wdebeaum/piano-keyboard/end.scad

/* end.scad - controls at the left end of octave.scad
 * William de Beaumont
 * 2020-06-28
 */

include <common.scad>;
include <logo.scad>;

//
// locations and sizes of PCB features
//

// reference point is top left corner of PCB; Y is inverted from KiCAD
// x->width, y->height, z->thickness

// the board itself
pcb_width = 1.62*25.4;
pcb_height = 3.23*25.4;

// Teensy 4.0
teensy_min_x = 0.87*25.4;
teensy_min_y = -0.45*25.4;
teensy_min_z = 0.1*25.4; // ???
teensy_width = 0.7*25.4;
teensy_height = 1.4*25.4;
teensy_thickness = pcb_thickness; // ???
// guessing based on pictures
teensy_led_x = teensy_min_x + 0.5*25.4;
teensy_led_y = teensy_min_y + 0.13*25.4;
teensy_led_radius = 0.1*25.4/2;

// USB receptacle on Teensy 4.0
// (mostly guesswork from generic USB diagram I googled)
usb_width = 7.5;
usb_height = 2.75+3.35;
usb_thickness = 2.5;
// guessing it's centered on Teensy
usb_min_x = teensy_min_x + (teensy_width - usb_width)/2;
usb_max_y = teensy_min_y + teensy_height + 1.3;
usb_min_z = teensy_min_z + teensy_thickness;

// connector to keys
j5_x = pcb_width;
j5_min_y = -1.62*25.4;
j5_height = 0.5*25.4;
j5_thickness = 0.1*25.4;
j5_min_z = -(pcb_thickness+j5_thickness);

// screws
screw1_x = 1.12*25.4;
screw1_y = -1.35*25.4;
screw2_x = 0.67*25.4;
screw2_y = -2.9*25.4;

// buttons
button_radius = 3.51/2; // radius of the part of the button that moves
button_thickness = 5; // height of the top of the button above the pcb
//button_travel = 0.010; // how much the button goes down when pressed
// ^^^ actual value vvv fudged
button_travel = 1.01;
button_width = 6; // width and height of the square box the button is in
// button centers:
//    x1  x2  x3
// y1     sw1
// y2     sw2
// y3 sw3     sw7
// y4     sw6
// y5 sw4
// y6     sw5
button_x1 = 0.24*25.4;
button_x2 = 0.7*25.4;
button_x3 = 1.15*25.4;
button_y1 = -1.24*25.4;
button_y2 = -1.59*25.4;
button_y3 = -1.84*25.4;
button_y4 = -2.1*25.4;
button_y5 = -2.28*25.4;
button_y6 = -2.47*25.4;

// potentiometers
pot_shaft_radius = 6/2;
pot_shaft_max_x = 0.005*25.4;
pot_shaft_length = 20-8; // quoted as 8mm, but that includes pot body
pot_shaft_min_x = pot_shaft_max_x - pot_shaft_length;
pot_flat_length = 7;
pot_flat_depth = 6-4.5; // how far in from where the circumference would be otherwise
pot1_shaft_y = -1.35*25.4;
pot2_shaft_y = -2.9*25.4;
pot_shaft_z = 0.394*25.4;
pot_base_width = 9.7; // along edge of pcb

// sustain pedal jack
sus_radius = 0.1875*25.4;
sus_x = 1.2730*25.4; // center x
sus_y = -pcb_height;
sus_z = 0.492*25.4;
sus_min_x = 0.96*25.4; // left x

// max height above pcb of any component (sustain pedal jack)
top_component_thickness = 0.708*25.4;
// ditto for components on bottom (J5)
//bottom_component_thickness = 0.1*25.4; //unused

//
// other parameters and computed values
//

electronics_height = pcb_height + teensy_height + teensy_min_y;
electronics_thickness = top_component_thickness + support_base_height;
electronics_min_z = -support_base_height;

pcb_y_gap = gap + small_v_hole_shrinkage;

knob_radius = 15;
knob_width = pot_shaft_length - (wall_thickness+2*(gap+sliding_deduction));
knob_min_x = pot_shaft_min_x;
// use thicker outer wall for knobs so that the gap doesn't show much
knob_wall_thickness = 5;
finger_radius = 5;
finger_depth = 2;
knob_ir = pot_shaft_radius + gap/* + small_v_hole_shrinkage*/ + thin_wall_deduction;

button_shaft_length = button_travel + gap + wall_thickness + gap + top_component_thickness - button_thickness;
shaft_radius = button_radius/sqrt(2)+small_v_hole_shrinkage/*fudge*/;
triangle_retention_radius = (shaft_radius + wall_thickness) / sqrt(2);
button_head_thickness = 2*wall_thickness;
button_head_width = 1.5*button_width; // for rectangle button
button_head_radius = button_head_width/(2*sqrt(2)); // for triangle buttons

shelf_width = 1.5; // not wide enough to interfere with solder joints around pcb edges

skewer_x = pcb_width/2; // start in middle of pcb width
skewer_length = skewer_x+10; // stick out 1cm from right side
skewer_y = // this depends on a lot of stuff that only it depends on in this file, so I'll just use the numbers without naming all of them:
  -(
  4*wall_thickness // distance from front edge of octave support to center of front skewer (thought this was 5*wt, but empirically it's 4?)
  +gap+thin_wall_deduction+sliding_deduction // support_gap; distance from back edge of octave pcb to front edge of support
  +0.83*25.4 // distance from back of octave pcb to back of connector
  )
  +1.08*25.4 // distance from back of end pcb to back of connector to octave
  ;
skewer_z = skewer_hole_radius+wall_thickness/2 - support_base_height;

screw_post_base_radius = sus_min_x - gap - screw2_x; // max it could be

button_panel_x = button_x2;
button_panel_y = button_y3;
button_panel_radius = button_panel_y - screw2_y + screw_post_base_radius;
button_panel_shelf_width = 3*wall_thickness;
button_panel_left_height = 2*(sqrt(button_panel_radius*button_panel_radius - button_panel_x*button_panel_x));

bottom_shelf_width = 10;

//
// non-printed parts
//

module end_pcb() {
    translate([0,0,-pcb_thickness/2])
  import("end-pcb/piano-keyboard-end-pcb.stl");
  // teensy
    translate([teensy_min_x, teensy_min_y, teensy_min_z])
  cube([teensy_width, teensy_height, teensy_thickness]);
  // usb
    translate([usb_min_x, usb_max_y - usb_height, usb_min_z])
  cube([usb_width, usb_height, usb_thickness]);
  // buttons shown on pcb aren't as tall as the ones I actually bought; add cylinders showing their real height
    translate([button_x2,button_y1,0])
  cylinder(r=button_radius, h=button_thickness);
    translate([button_x2,button_y2,0])
  cylinder(r=button_radius, h=button_thickness);
    translate([button_x1,button_y3,0])
  cylinder(r=button_radius, h=button_thickness);
    translate([button_x3,button_y3,0])
  cylinder(r=button_radius, h=button_thickness);
    translate([button_x2,button_y4,0])
  cylinder(r=button_radius, h=button_thickness);
    translate([button_x1,button_y5,0])
  cylinder(r=button_radius, h=button_thickness);
    translate([button_x2,button_y6,0])
  cylinder(r=button_radius, h=button_thickness);
}

module end_cardboard() {
  difference() {
      translate([
	-(wall_thickness+gap),
	-(wall_thickness+pcb_y_gap+pcb_height),
	-(support_base_height+gap+cardboard_thickness)
      ])
    cube([
      wall_thickness+gap+pcb_width,
      2*(wall_thickness+pcb_y_gap)+pcb_height+teensy_height+teensy_min_y,
      cardboard_thickness
    ]);
    // top left bevel
      translate([teensy_min_x-(gap+wall_thickness),teensy_min_y+teensy_height+gap+wall_thickness,0])
      rotate([0,0,-45])
      translate([-50,0,0])
    cube([100,100,100], center=true);
    echo(
      cardboard_x=
      wall_thickness+gap+pcb_width,
      cardboard_y=
      2*(wall_thickness+pcb_y_gap)+pcb_height+teensy_height+teensy_min_y,
      cardboard_bevel=
      teensy_min_x
    );
  }
}

//
// main enclosure
//

module enclosure() {
  difference() {
    // main body
      translate([-(gap+wall_thickness), -(pcb_height+pcb_y_gap+wall_thickness), electronics_min_z-epsilon])
    cube([pcb_width+gap+wall_thickness, electronics_height+2*(pcb_y_gap+wall_thickness), electronics_thickness+gap+wall_thickness+epsilon]);
    // main hollow
      translate([-gap, -(pcb_height+pcb_y_gap), electronics_min_z-gap])
    cube([pcb_width+gap+epsilon, pcb_height+2*pcb_y_gap, electronics_thickness+2*gap]);
    // teensy hollow
      translate([teensy_min_x-gap, teensy_min_y, 0])
    cube([pcb_width-teensy_min_x+gap+epsilon, teensy_height+pcb_y_gap, usb_min_z+usb_thickness+gap]);
    hole_thickness = wall_thickness+2*epsilon;
    // top left bevel
      translate([teensy_min_x-(gap+wall_thickness),teensy_min_y+teensy_height+gap+wall_thickness,0])
      rotate([0,0,-45])
      translate([-50,0,0])
    cube([100,100,100], center=true);
    // top...top? bevel
      translate([0,teensy_min_y+teensy_height+gap+wall_thickness,usb_min_z+usb_thickness+gap+wall_thickness])
      rotate([-27.1,0,0]) // manually tuned so edges line up
      translate([0,0,50])
    cube([100,100,100], center=true);
    // front skewer hole (end doesn't reach far enough back for the back one)
      translate([skewer_x-gap,skewer_y,skewer_z])
      rotate([0,90,0])
    cylinder(r=skewer_hole_radius/*+small_v_hole_shrinkage*/, h=skewer_length+gap);
    // hole for usb receptacle
      translate([usb_min_x-gap, usb_max_y-hole_thickness+epsilon+0.25/*fudge for pcb_y_gap*/, usb_min_z-gap])
    cube([usb_width+2*gap /*extend for assemblability*/+50, hole_thickness, usb_thickness+2*gap]);
    // hole for led (light pipe?)
      translate([teensy_led_x, teensy_led_y, top_component_thickness+gap-epsilon])
    cylinder(r=teensy_led_radius, h=hole_thickness);
    // hole for sustain pedal jack
      translate([sus_x, sus_y-pcb_y_gap+epsilon, sus_z])
      rotate([90,0,0])
    cylinder(r=sus_radius+gap, h=hole_thickness);
    // ...extend for assemblability
      translate([sus_x, sus_y-(pcb_y_gap+wall_thickness+epsilon), sus_z-(sus_radius+gap)])
    cube([50, hole_thickness, 2*(sus_radius+gap)]);
    // holes for pots
      translate([epsilon-gap, pot1_shaft_y, pot_shaft_z])
      rotate([0,-90,0])
    cylinder(r=pot_shaft_radius+gap+sliding_deduction, h=hole_thickness);
      translate([epsilon-gap, pot2_shaft_y, pot_shaft_z])
      rotate([0,-90,0])
    cylinder(r=pot_shaft_radius+gap+sliding_deduction, h=hole_thickness);
    // hole for pitch bend torsion spring anchoring
      translate([-(wall_thickness+gap+epsilon), pot2_shaft_y-2*(insulated_wire_radius+gap), top_component_thickness - wall_thickness - 2*(insulated_wire_radius+gap)])
    cube([hole_thickness, 4*(insulated_wire_radius+gap), 2*(insulated_wire_radius+gap)]);
    // hole for button panel
      translate([button_panel_x, button_panel_y, top_component_thickness-epsilon])
    cylinder(r=button_panel_radius+gap, h=hole_thickness+gap, $fn=48);
  }
  // shelves around edge of pcb
  // ..bottom
  // ....under pcb
    translate([-(gap+epsilon), -(pcb_height+pcb_y_gap+epsilon), -support_base_height])
  cube([pcb_width+gap+epsilon, shelf_width+epsilon, support_base_height-(pcb_thickness+gap)]);
  // ....over pcb
    translate([-(gap+epsilon), -(pcb_height+pcb_y_gap+epsilon), gap])
  cube([pcb_width+gap+epsilon, shelf_width+epsilon, shelf_width]);
  // ..left
  // ....under pcb
    translate([-(gap+epsilon), -pcb_height, -support_base_height])
  cube([shelf_width+epsilon, pcb_height, support_base_height-(pcb_thickness+gap)]);
  // ......farther under pcb, for strength against bending the left wall
    translate([-(gap+epsilon), -pcb_height, -support_base_height])
  cube([bottom_shelf_width+epsilon, pcb_height, wall_thickness]);
    translate([2*bottom_shelf_width-(gap+epsilon), bottom_shelf_width+shelf_width-(epsilon+pcb_y_gap+pcb_height), -support_base_height])
    rotate([0,0,180])
  difference() {
    cube([bottom_shelf_width+epsilon, bottom_shelf_width+epsilon, wall_thickness]);
      translate([0,0,-epsilon])
    cylinder(r=bottom_shelf_width, h=wall_thickness+2*epsilon);
  }
    translate([2*bottom_shelf_width-(gap+epsilon), epsilon+pcb_y_gap-(bottom_shelf_width+shelf_width), -support_base_height])
    rotate([0,0,90])
  difference() {
    cube([10+epsilon, 10+epsilon, wall_thickness]);
      translate([0,0,-epsilon])
    cylinder(r=10, h=wall_thickness+2*epsilon);
  }
  // ....over pcb (with cutouts for pots)
  difference() {
      translate([-(gap+epsilon), -pcb_height, gap])
    cube([shelf_width+epsilon, pcb_height, shelf_width]);
    // pot cutouts
      translate([0,pot1_shaft_y,0])
    cube([100,pot_base_width+2*gap,100], center=true);
      translate([0,pot2_shaft_y,0])
    cube([100,pot_base_width+2*gap,100], center=true);
  }
  // ..top
  // ....under pcb
    translate([-(gap+epsilon), -shelf_width+pcb_y_gap+epsilon, -support_base_height])
  cube([skewer_x+epsilon, shelf_width+pcb_y_gap+epsilon, support_base_height-(pcb_thickness+gap)]);
  // ....over pcb
    translate([-(gap+epsilon), -shelf_width+pcb_y_gap+epsilon, gap])
  cube([teensy_min_x+epsilon, shelf_width+epsilon, shelf_width]);
  // TODO? shelves around teensy (I don't know its position as accurately, nor how wide its shelves should be)
  // shelf around button panel
  difference() {
    $fn=48;
    intersection() {
	translate([button_panel_x, button_panel_y, top_component_thickness-wall_thickness])
      cylinder(r=button_panel_radius+gap+wall_thickness, h=wall_thickness+gap+epsilon);
	translate([-(gap+wall_thickness), -(pcb_height+gap+wall_thickness), electronics_min_z-epsilon])
      cube([pcb_width+gap+wall_thickness, electronics_height+2*(gap+wall_thickness), electronics_thickness+gap+wall_thickness+epsilon]);
    }
    // center hole
      translate([button_panel_x, button_panel_y, top_component_thickness-wall_thickness-epsilon])
    cylinder(r=button_panel_radius-button_panel_shelf_width, h=wall_thickness+gap+3*epsilon);
      translate([button_panel_x, button_panel_y, top_component_thickness-epsilon])
    cylinder(r=button_panel_radius+gap, h=gap+3*epsilon);
    // cutout for sustain pedal jack
      translate([sus_min_x - gap, button_panel_y - (button_panel_radius + wall_thickness + epsilon), top_component_thickness-wall_thickness-epsilon])
    cube([gap + pcb_width - sus_min_x + epsilon, button_panel_radius + epsilon, wall_thickness+gap+3*epsilon]);
    // cutout for front screw
      translate([screw2_x, screw2_y, top_component_thickness-wall_thickness-epsilon])
    cylinder(r=screw_post_base_radius+gap, h=wall_thickness+gap+3*epsilon);
  }
    translate([epsilon-(gap+wall_thickness), button_panel_y-button_panel_left_height/2, top_component_thickness-wall_thickness])
  cube([button_panel_shelf_width-epsilon, button_panel_left_height, wall_thickness]);
  // logo on top
    translate([25,3,top_component_thickness+gap+wall_thickness])
    rotate([0,0,180])
  logo();
}

module plated_enclosure() {
    rotate([0,-90,0])
    translate([wall_thickness+gap,0,0])
  enclosure();
}

//
// button extensions
//

module plated_rectangle_button() {
  intersection() {
    union() {
      // user side flat
        translate([-button_head_width/2,-button_head_thickness,0])
      cube([button_head_width, button_head_thickness, button_radius+small_v_hole_shrinkage/*fudge*/]);
      // shaft
        translate([-button_radius, -epsilon, 0])
      cube([2*button_radius, button_shaft_length+epsilon, button_radius+small_v_hole_shrinkage/*fudge*/]);
      // pcb side retention
        translate([-(button_radius+wall_thickness),button_shaft_length-wall_thickness,0])
      cube([2*(button_radius+wall_thickness), wall_thickness, button_radius+small_v_hole_shrinkage/*fudge*/]);
    }
      translate([-50,-button_head_thickness,0])
    cube([100, button_shaft_length+button_head_thickness, 100]);
  }
}

module rectangle_button() {
    translate([0,0, top_component_thickness+gap+wall_thickness+gap])
    rotate([-90,0,0])
    translate([0,0,-button_radius/2])
  plated_rectangle_button();
}

module plated_triangle_button() {
  intersection() {
    union() {
      // user side flat
        rotate([0,45,0])
        translate([-button_head_radius,-button_head_thickness,-button_head_radius])
      cube([2*button_head_radius, button_head_thickness, 2*button_head_radius]);
      // shaft
        rotate([0,45,0])
	translate([-shaft_radius,-epsilon,-shaft_radius])
      cube([2*shaft_radius, button_shaft_length+epsilon, 2*shaft_radius]);
      // pcb side retention
        rotate([0,45,0])
	translate([-triangle_retention_radius,button_shaft_length-wall_thickness,-triangle_retention_radius])
      cube([2*triangle_retention_radius, wall_thickness, 2*triangle_retention_radius]);
    }
      translate([-50,-button_head_thickness,0])
    cube([100, button_shaft_length+button_head_thickness, 100]);
  }
}

module triangle_button() {
    translate([0,0, top_component_thickness+gap+wall_thickness+gap])
    rotate([-90,0,0])
    translate([0,0,-shaft_radius/2])
  plated_triangle_button();
}

//
// top panel with holes for buttons and screws
//

module rectangle_hole() {
  minkowski() {
    rectangle_button();
    cylinder(r=gap+sliding_deduction/*+small_v_hole_shrinkage*/, h=gap+sliding_deduction);
  }
}

module triangle_hole() {
  minkowski() {
    triangle_button();
    cylinder(r=gap+sliding_deduction/*+small_v_hole_shrinkage*/, h=gap+sliding_deduction);
  }
}

module screw_post() {
    translate([0, 0, gap])
  difference() {
    cylinder(r1=support_hole_or, r2=screw_post_base_radius, h=top_component_thickness+epsilon);
      translate([0,0,-epsilon])
    cylinder(r=support_hole_ir, h=screw_threads_height);
  }
}

module button_panel() {
  difference() {
    union() {
      intersection() {
	  translate([button_panel_x, button_panel_y, top_component_thickness+gap])
	cylinder(r=button_panel_radius, h=wall_thickness, $fn=48);
	  translate([-(gap+wall_thickness), -(pcb_height+gap+wall_thickness), electronics_min_z-epsilon])
	cube([pcb_width+gap+wall_thickness, electronics_height+2*(gap+wall_thickness), electronics_thickness+gap+wall_thickness+epsilon]);
      }
      // button shaft guides
      button_shaft_guide_min_z = button_thickness + gap + wall_thickness + gap + sliding_deduction;
      button_shaft_guide_thickness = top_component_thickness + gap - button_shaft_guide_min_z + epsilon;
      button_shaft_guide_width = button_width + 2*wall_thickness;
      // ...horizontal
        translate([
	  button_x1 - button_width/2 - wall_thickness,
	  button_y3 - button_shaft_guide_width/2,
	  button_shaft_guide_min_z
	])
      cube([
        button_width + button_x3 - button_x1 + wall_thickness,
	button_shaft_guide_width,
	button_shaft_guide_thickness
      ]);
      // ...vertical
        translate([
	  button_x2 - button_shaft_guide_width/2,
	  button_y6 - button_width/2,
	  button_shaft_guide_min_z
	])
      cube([
        button_shaft_guide_width,
	button_width + button_y1 - button_y6,
	button_shaft_guide_thickness
      ]);
      // ...lower left
        translate([
	  button_x1 - button_shaft_guide_width/2,
	  button_y5 - button_width/2,
	  button_shaft_guide_min_z
	])
      cube([
        button_shaft_guide_width/2 + button_x2 - button_x1,
	button_width/2 + button_y3 - button_y5,
	button_shaft_guide_thickness
      ]);
    }
    // holes for button shafts
    translate([button_x2, button_y1, 0]) triangle_hole();
    translate([button_x2, button_y2, 0]) triangle_hole();
    translate([button_x1, button_y3, 0]) rotate([0,0,90]) triangle_hole();
    translate([button_x3, button_y3, 0]) rotate([0,0,-90]) triangle_hole();
    translate([button_x2, button_y4, 0]) rotate([0,0,180]) triangle_hole();
    translate([button_x1, button_y5, 0]) rectangle_hole();
    translate([button_x2, button_y6, 0]) rotate([0,0,180]) triangle_hole();
  }
  // screw hole posts
  translate([screw1_x, screw1_y, 0]) screw_post();
  translate([screw2_x, screw2_y, 0]) screw_post();
}

module plated_button_panel() {
    translate([60,0,top_component_thickness+gap+wall_thickness])
    rotate([0,180,0])
  button_panel();
}

//
// mod/pitch pot knob
//

module knob() {
  difference() {
    union() {
      // outer body
      difference() {
	union() {
	  // left bevel
	  cylinder(r1=knob_radius-wall_thickness, r2=knob_radius, h=wall_thickness+epsilon);
	    translate([0,0,wall_thickness])
	  // main cylinder
	  cylinder(r=knob_radius, h=knob_width-2*wall_thickness);
	  // right bevel
	    translate([0,0,knob_width-(wall_thickness+epsilon)])
	  cylinder(r1=knob_radius, r2=knob_radius-wall_thickness, h=wall_thickness+epsilon);
	}
	  translate([0,0,wall_thickness])
	cylinder(r=knob_radius-knob_wall_thickness, h=knob_width-wall_thickness+epsilon);
	// finger notch
	  translate([-(knob_radius+finger_radius-finger_depth), 0, -epsilon])
	cylinder(r=finger_radius, h=knob_width+2*epsilon);
	// anchor for torson spring for pitch bend knob
	// bottom hole
	  translate([
	    knob_radius - (knob_wall_thickness+1),
	    -(insulated_wire_radius+gap),
	    (knob_width - (wall_thickness + 4*(insulated_wire_radius+gap)))/2
	  ])
	cube([
	  knob_wall_thickness+1/*fudge for curvature*/,
	  2*(insulated_wire_radius+gap),
	  2*(insulated_wire_radius+gap)
	]);
	// top hole
	  translate([
	    knob_radius - (knob_wall_thickness+1),
	    -(insulated_wire_radius+gap),
	    (knob_width + wall_thickness)/2
	  ])
	cube([
	  knob_wall_thickness+1/*fudge for curvature*/,
	  2*(insulated_wire_radius+gap),
	  2*(insulated_wire_radius+gap)
	]);
	// outer trench
	  translate([
	    knob_radius - 2*(insulated_wire_radius+gap),
	    -(insulated_wire_radius+gap),
	    (knob_width - (wall_thickness+4*(insulated_wire_radius+gap)))/2
	  ])
	cube([
	  2*(insulated_wire_radius+gap)+epsilon,
	  2*(insulated_wire_radius+gap),
	  wall_thickness+4*(insulated_wire_radius+gap)
	]);
      }
      // inner post
      cylinder(r=knob_ir+wall_thickness, h=knob_width);
    }
    // shaft hole
      translate([0,0,-epsilon])
    difference() {
      cylinder(r=knob_ir, h=knob_width+2*epsilon);
      // flat
	rotate([0,0,-90])
        translate([
	  -(knob_ir+epsilon),
	  knob_ir-pot_flat_depth,
	  -2*epsilon
	])
      cube([
        2*(knob_ir+epsilon),
        2*(knob_ir+epsilon),
        pot_flat_length - gap + 2*epsilon
      ]);
    }
  }
}

module white_plated() {
  plated_enclosure();
  plated_button_panel();
}

module buttons_plated() {
    translate([40,-25,0])
  plated_rectangle_button();
  for(x=[30:10:50]) {
      translate([x,-5,0])
    plated_triangle_button();
      translate([x,-45,0])
    plated_triangle_button();
  }
}

module black_plated() {
    translate([0,0,0])
  knob();
    translate([0,-40,0])
  knob();
  buttons_plated();
}

module assembled_end() {
  %end_pcb();
    %translate([screw1_x,screw1_y,-(pcb_thickness+gap)])
    rotate([180,0,0])
  screw();
    %translate([screw2_x,screw2_y,-(pcb_thickness+gap)])
    rotate([180,0,0])
  screw();
  enclosure();
  button_panel();
  translate([button_x2, button_y1, 0]) triangle_button();
  translate([button_x2, button_y2, 0]) triangle_button();
  translate([button_x1, button_y3, 0]) rotate([0,0,90]) triangle_button();
  translate([button_x3, button_y3, 0]) rotate([0,0,-90]) triangle_button();
  translate([button_x2, button_y4, 0]) rotate([0,0,180]) triangle_button();
  translate([button_x1, button_y5, 0]) rectangle_button();
  translate([button_x2, button_y6, 0]) rotate([0,0,180]) triangle_button();
    %translate([skewer_x, skewer_y, skewer_z])
    rotate([0,90,0])
  cylinder(r=skewer_radius, h=skewer_length);
  echo(skewer_length=skewer_length);
    translate([pot_shaft_min_x, pot1_shaft_y, pot_shaft_z])
    rotate([0,90,0])
  knob();
    translate([pot_shaft_min_x, pot2_shaft_y, pot_shaft_z])
    rotate([0,90,0])
  knob();
  %end_cardboard();
}

// helper for doing assembly steps; step(n) is 1 before the step starts, 0 after the step ends, and linear during the step
num_steps = 8;
function step(n) =
  ($t < n/num_steps ? 1 : // before
  ($t > (n+1)/num_steps ? 0 : // after
  1 - ($t - n/num_steps) * num_steps)); // during

/* steps:
0	pcb
1	button panel
2	screws
3	buttons
4	knobs
5	skewer
6	cardboard
7	finished!
*/

module exploded_end() {
    translate([step(0)*(pcb_width+10),0,0])
  %end_pcb();
    %translate([0,0,step(2)*-(screw_threads_height+10)])
    translate([screw1_x,screw1_y,-(pcb_thickness+gap)])
    rotate([180,0,0])
  screw();
    %translate([0,0,step(2)*-(screw_threads_height+10)])
    translate([screw2_x,screw2_y,-(pcb_thickness+gap)])
    rotate([180,0,0])
  screw();
  enclosure();
    translate([0,0,step(1)*(top_component_thickness+10)])
  button_panel();
    translate([0,0,step(3)*2*(top_component_thickness+10)])
  union() {
    translate([button_x2, button_y1, 0]) triangle_button();
    translate([button_x2, button_y2, 0]) triangle_button();
    translate([button_x1, button_y3, 0]) rotate([0,0,90]) triangle_button();
    translate([button_x3, button_y3, 0]) rotate([0,0,-90]) triangle_button();
    translate([button_x2, button_y4, 0]) rotate([0,0,180]) triangle_button();
    translate([button_x1, button_y5, 0]) rectangle_button();
    translate([button_x2, button_y6, 0]) rotate([0,0,180]) triangle_button();
  }
    %translate([step(5)*(2*(pcb_width+10)-skewer_x),0,0])
    translate([skewer_x, skewer_y, skewer_z])
    rotate([0,90,0])
  cylinder(r=skewer_radius, h=skewer_length);
    translate([step(4)*-(knob_width+10),0,0])
    translate([pot_shaft_min_x, pot1_shaft_y, pot_shaft_z])
    rotate([0,90,0])
  knob();
    translate([step(4)*-(knob_width+10),0,0])
    translate([pot_shaft_min_x, pot2_shaft_y, pot_shaft_z])
    rotate([0,90,0])
  knob();
    %translate([0,0,step(6)*-20])
  end_cardboard();
}

//exploded_end();
assembled_end();
//white_plated();
//black_plated();
